ZHANGMINGMIAO/DIYSON-FOR-MDS/PCB/Snipaste_2023-03-19_16-48-15.png

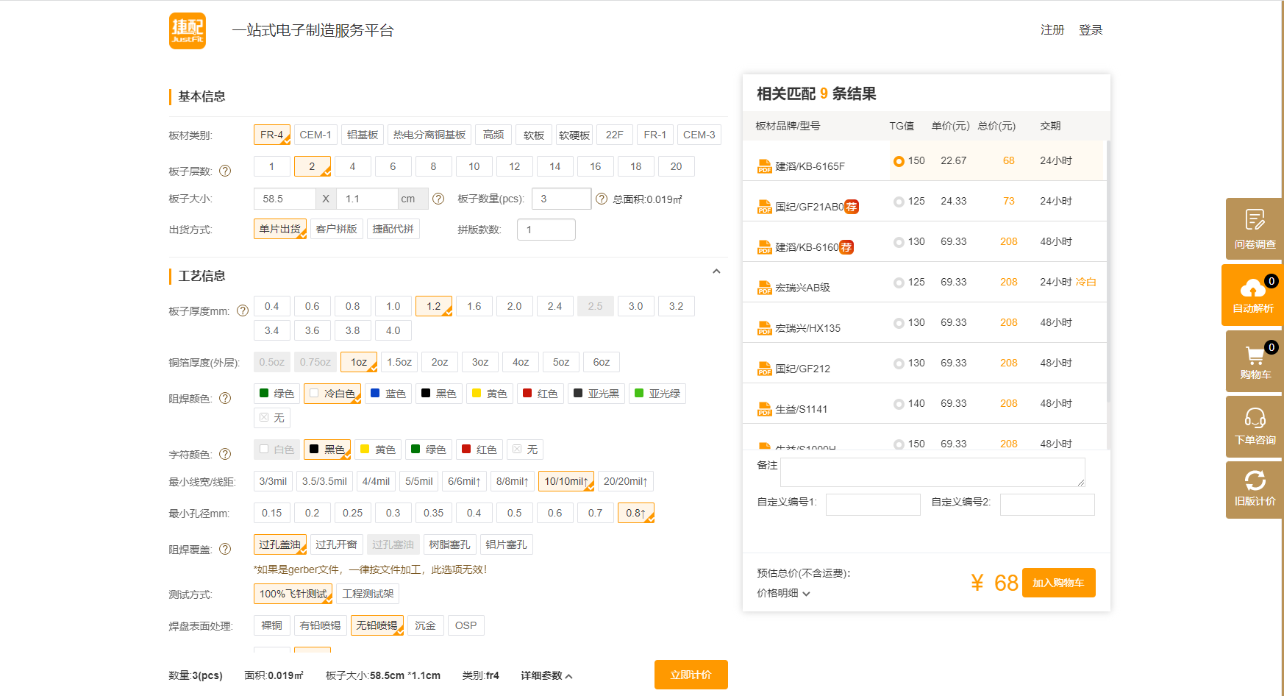
PCB/Snipaste_2023-03-19_16-48-15.png
