ZHANGMINGMIAO/DIYSON-FOR-MDS/PCB/Snipaste_2023-03-19_16-50-18.png

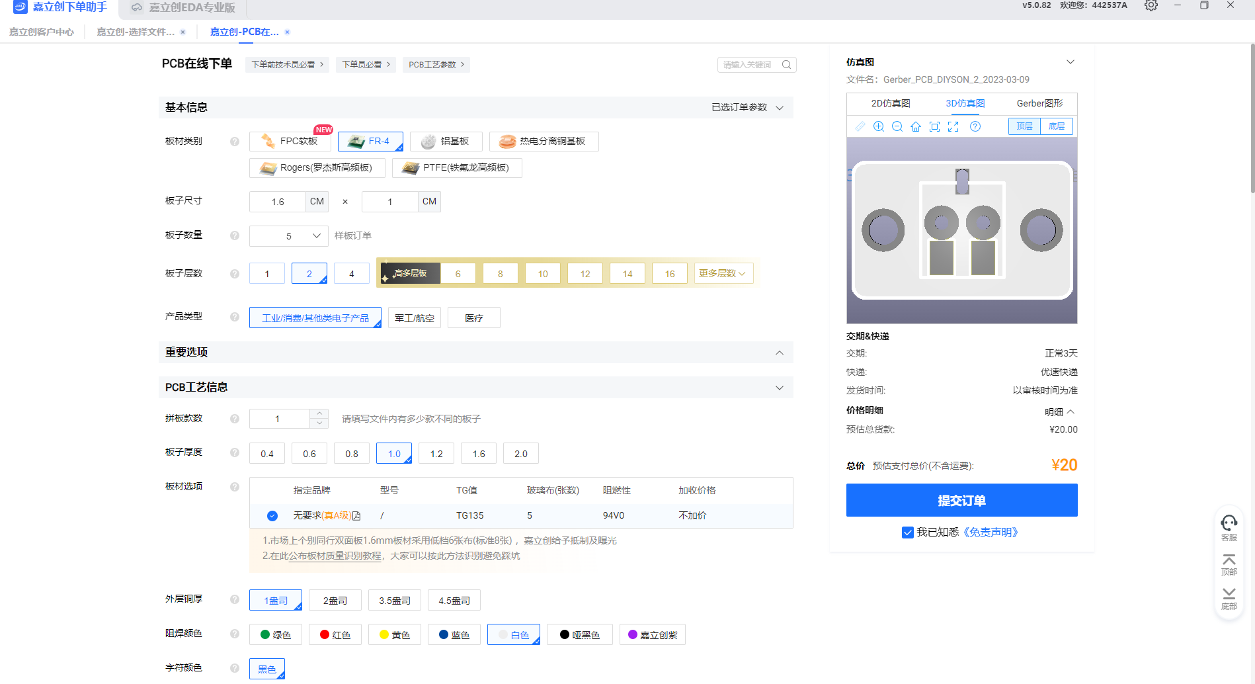
PCB/Snipaste_2023-03-19_16-50-18.png
