ZHANGMINGMIAO/DIYSON-FOR-MDS/Picture/DIYSON.10.png

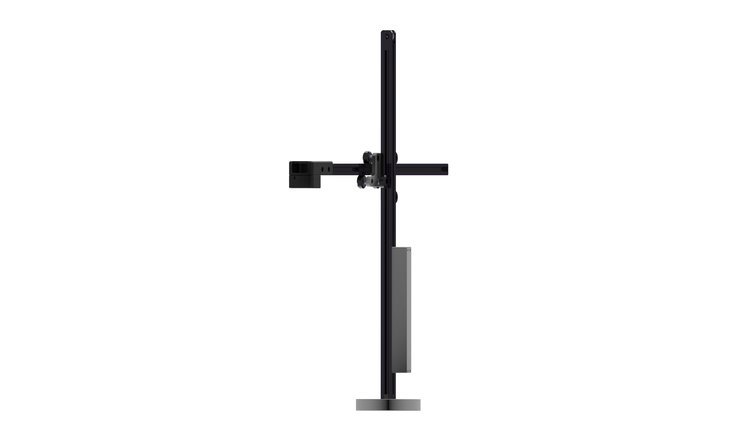
Picture/DIYSON.10.png
