ZHANGMINGMIAO/DIYSON-FOR-MDS/STL/Coutnterweight Enclosure.STL

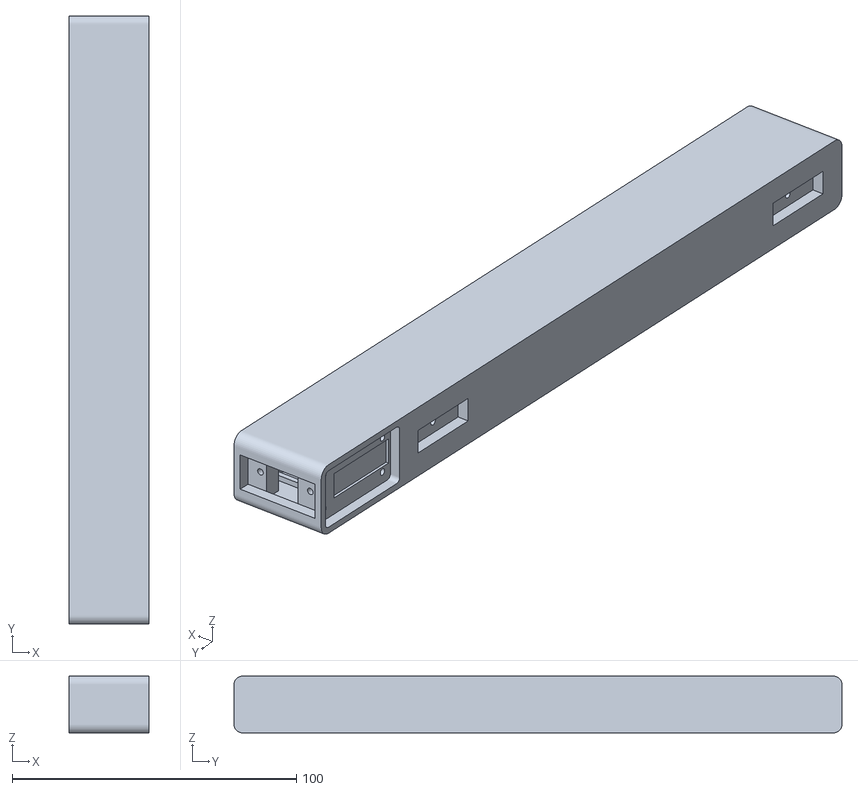
[picture p23: CAD file, 2023-05-03]
STL/Coutnterweight Enclosure.STL
28.0 x 214.0 x 20.0
