ZHANGMINGMIAO/DIYSON-FOR-MDS/STL/灯头底盖.STL

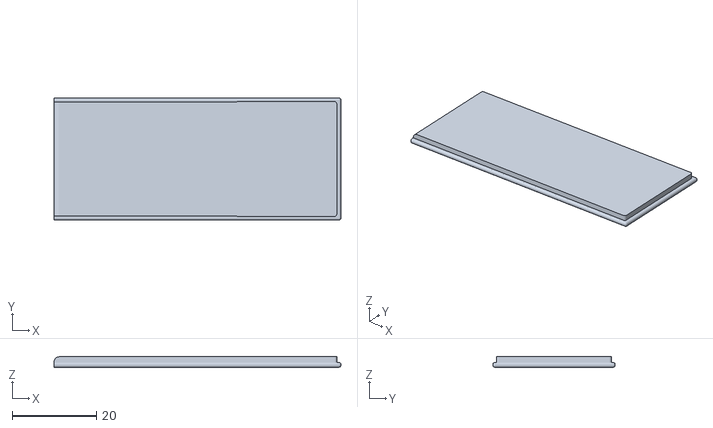
[picture p24: CAD file, 2023-05-03]
STL/灯头底盖.STL
68.0 x 29.0 x 2.50
