ZHANGMINGMIAO/DIYSON-FOR-MDS/slprt/Carriage2.SLDPRT

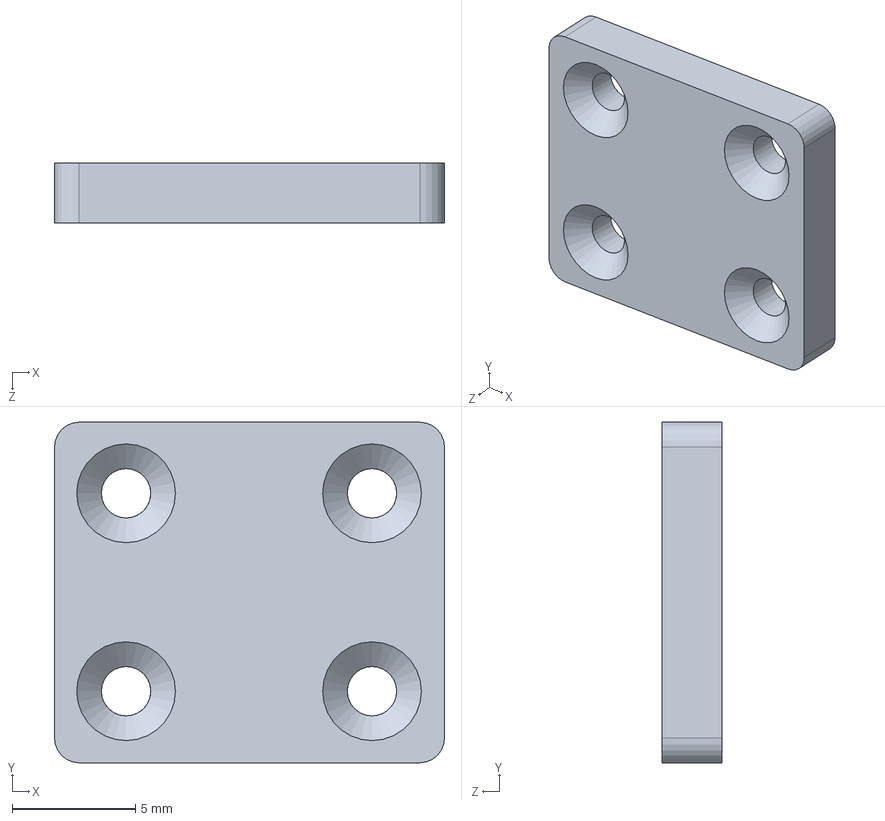
[picture p25: CAD file, 2023-05-03]
slprt/Carriage2.SLDPRT
15.8 x 13.8 x 2.45 mm
