ZHANGMINGMIAO/DIYSON-FOR-MDS/STL/灯头.STL

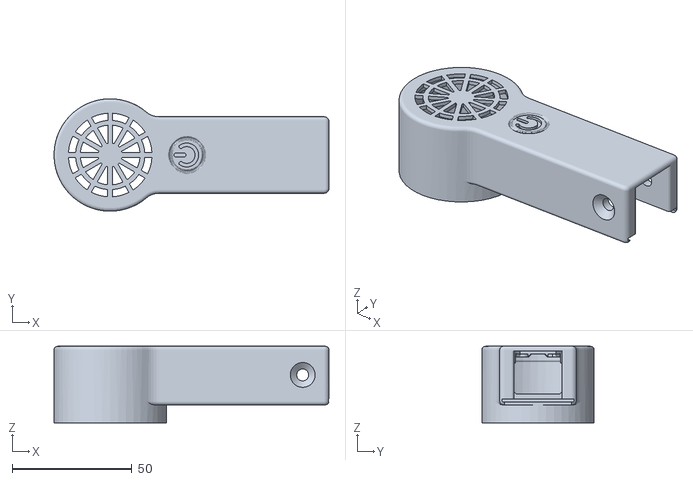
[picture p26: CAD file, 2023-05-03]
STL/灯头.STL
115.0 x 47.0 x 32.0
