ZHANGMINGMIAO/DIYSON-FOR-MDS/slprt/灯头底盖.sldprt

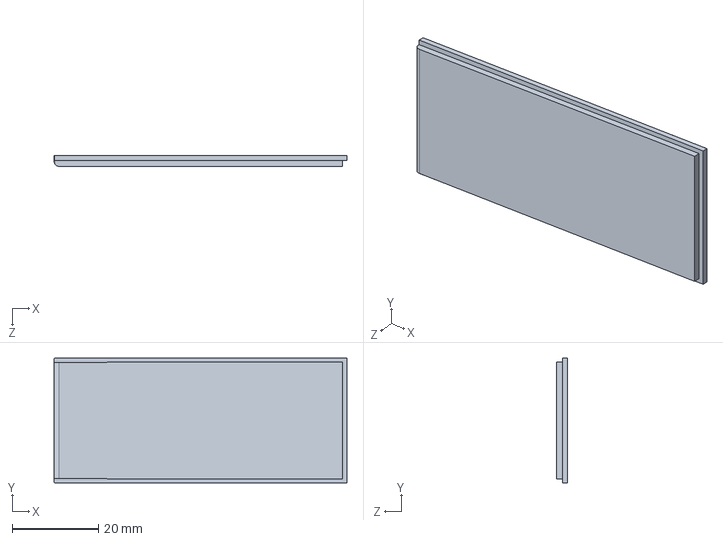
[picture p27: CAD file, 2023-05-03]
slprt/灯头底盖.sldprt
68.0 x 29.0 x 2.50 mm
