ZHANGMINGMIAO/DIYSON-FOR-MDS/slprt/Base2.sldprt

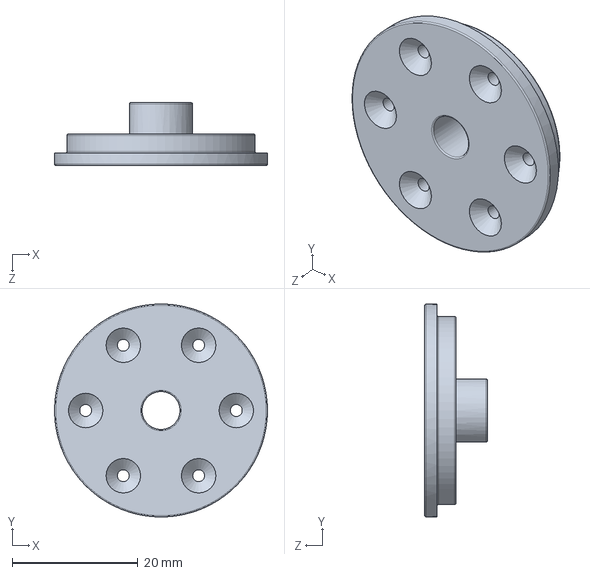
[picture p28: CAD file, 2023-05-03]
slprt/Base2.sldprt
33.9 x 33.9 x 10.0 mm
