ZHANGMINGMIAO/DIYSON-FOR-MDS/STL/Flex Tab.STL

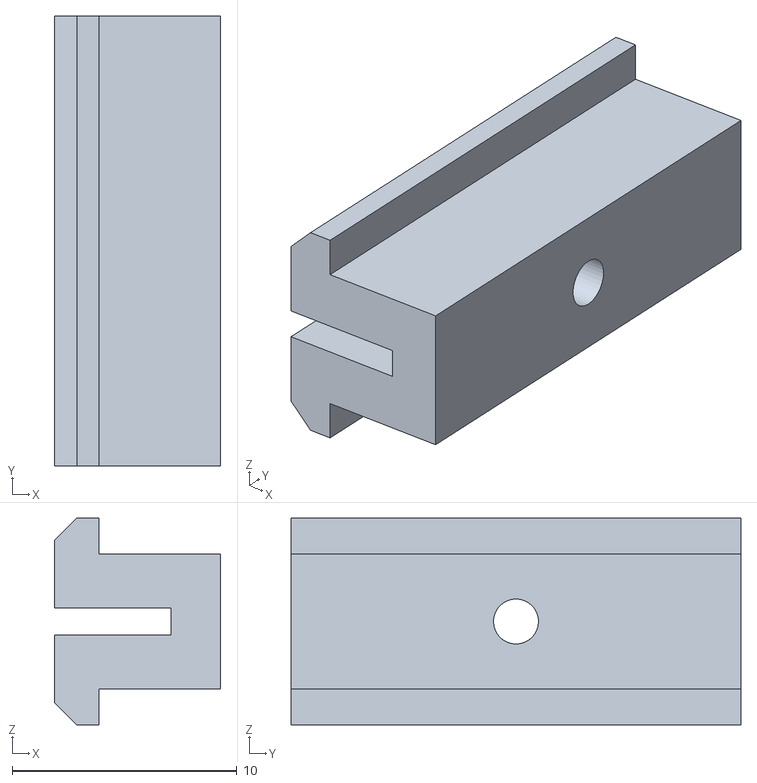
[picture p29: CAD file, 2023-03-19]
STL/Flex Tab.STL
7.40 x 20.0 x 9.20
