ZHANGMINGMIAO/DIYSON-FOR-MDS/STL/Pulley Mount.STL

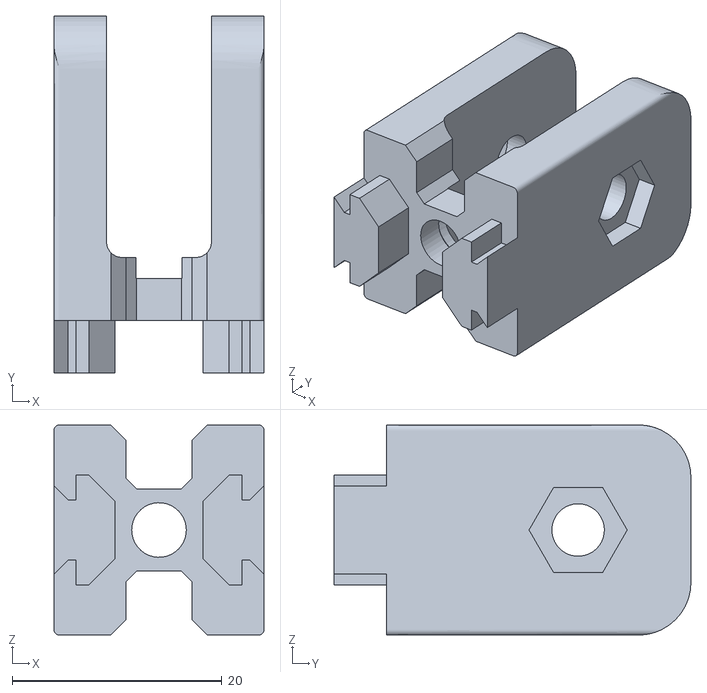
[picture p30: CAD file, 2023-03-16]
STL/Pulley Mount.STL
20.0 x 34.0 x 20.0
