ZHANGMINGMIAO/DIYSON-FOR-MDS/STL/End Cap.STL

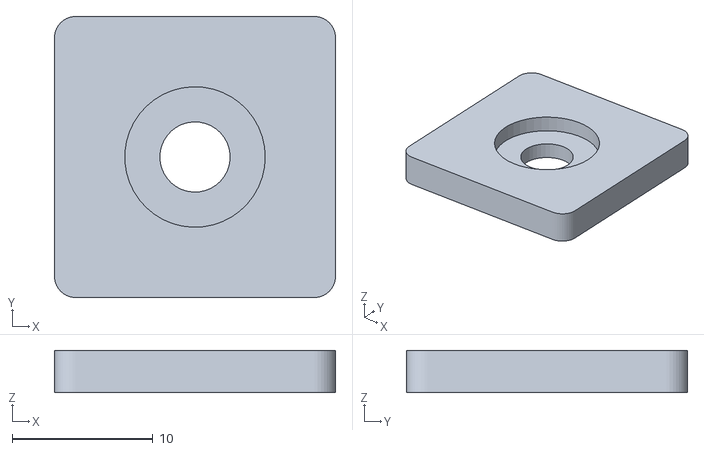
[picture p31: CAD file, 2023-03-16]
STL/End Cap.STL
20.0 x 20.0 x 3.00
