ZHANGMINGMIAO/DIYSON-FOR-MDS/STL/Counterweight Belt Clip.STL

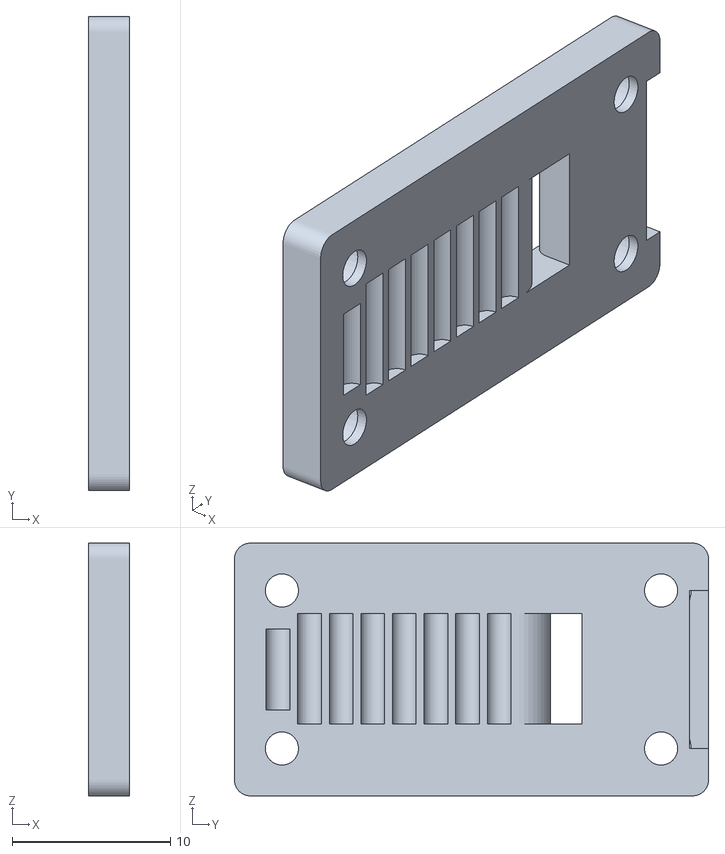
[picture p32: CAD file, 2023-03-16]
STL/Counterweight Belt Clip.STL
2.60 x 30.0 x 16.0
