ZHANGMINGMIAO/DIYSON-FOR-MDS/STL/Coutnterweight Lid.STL

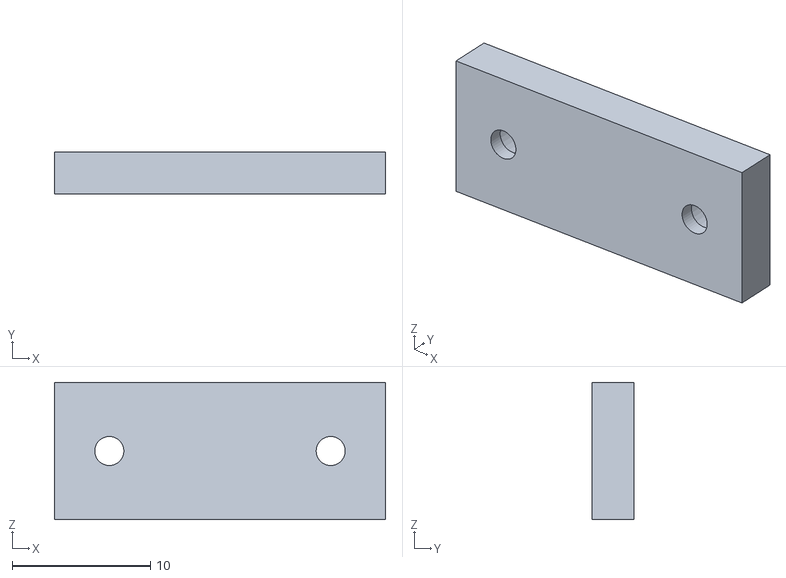
[picture p33: CAD file, 2023-03-16]
STL/Coutnterweight Lid.STL
23.9 x 3.00 x 9.92
