ZHANGMINGMIAO/DIYSON-FOR-MDS/slprt/2020V 铝型材.sldprt

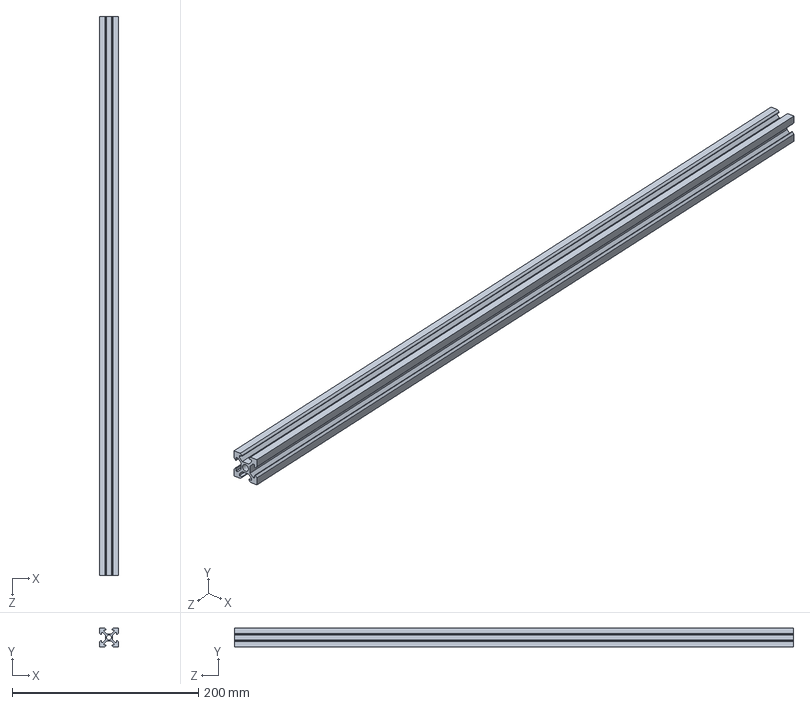
[picture p34: CAD file, 2023-03-16]
slprt/2020V 铝型材.sldprt
20.0 x 20.0 x 600.0 mm
