ZHANGMINGMIAO/DIYSON-FOR-MDS/slprt/6206ZZ轴承.SLDPRT

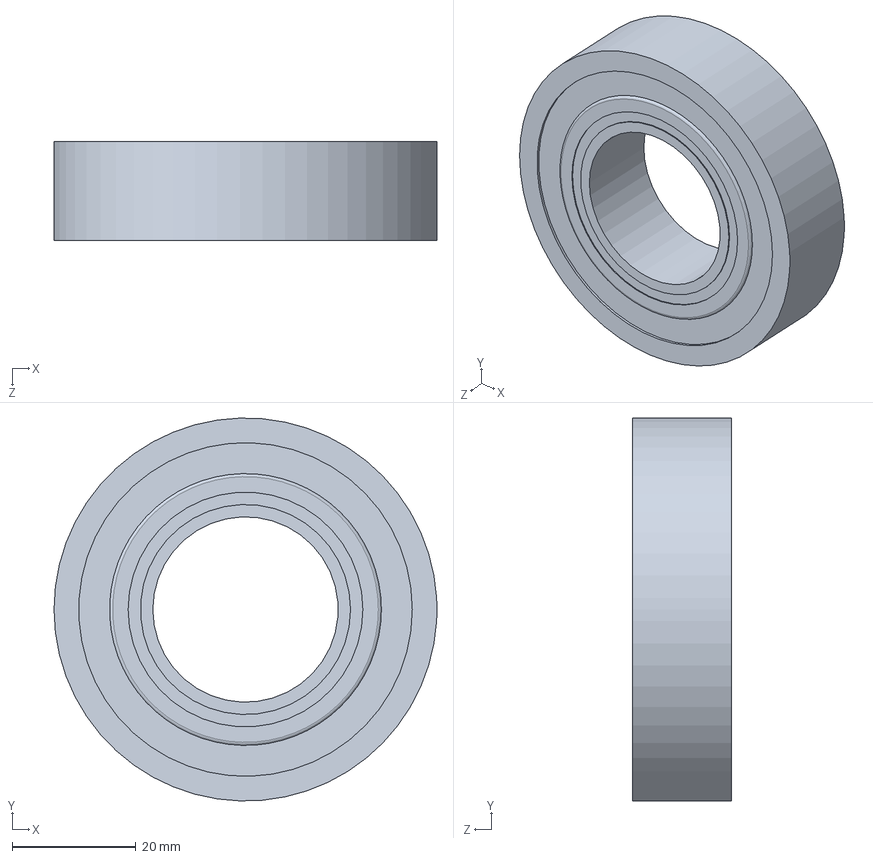
[picture p35: CAD file, 2023-03-16]
slprt/6206ZZ轴承.SLDPRT
62.0 x 62.0 x 16.0 mm
