ZHANGMINGMIAO/DIYSON-FOR-MDS/slprt/按键盖板.sldprt

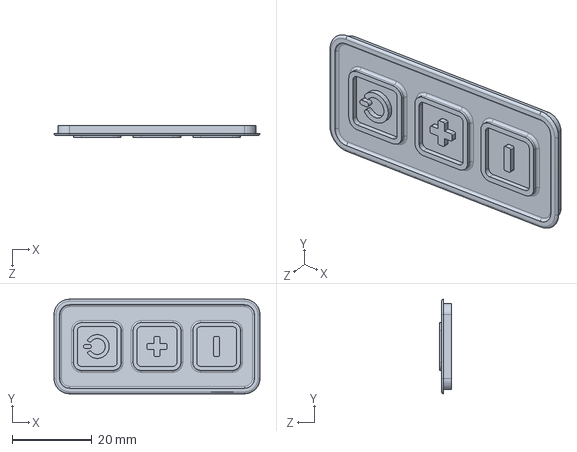
[picture p36: CAD file, 2023-03-16]
slprt/按键盖板.sldprt
51.8 x 23.8 x 3.00 mm
