ZHANGMINGMIAO/DIYSON-FOR-MDS/slprt/散热器3820.SLDPRT

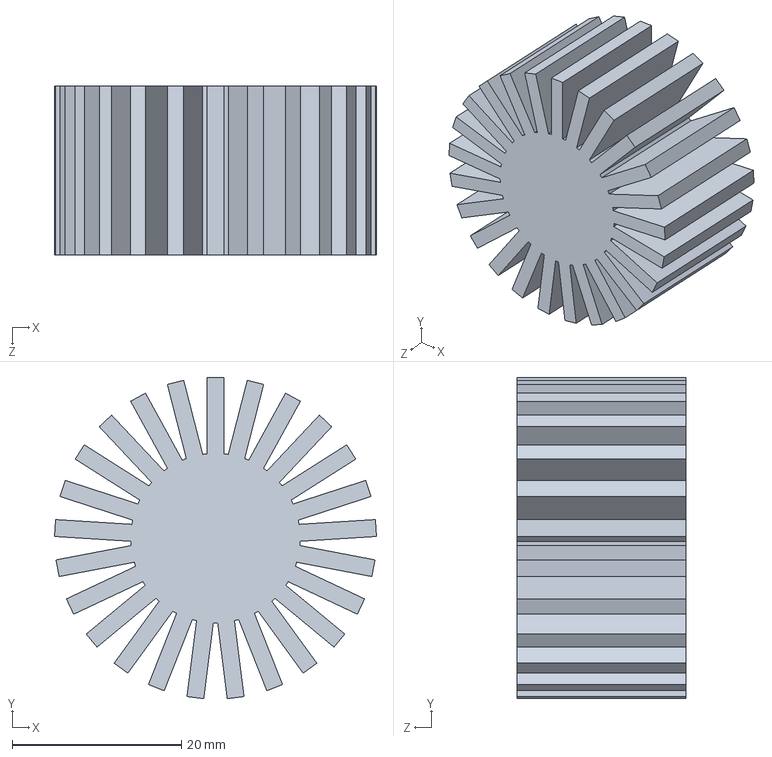
[picture p37: CAD file, 2023-03-16]
slprt/散热器3820.SLDPRT
38.0 x 37.9 x 20.0 mm
