ZHANGMINGMIAO/DIYSON-FOR-MDS/slprt/风扇3010.SLDPRT

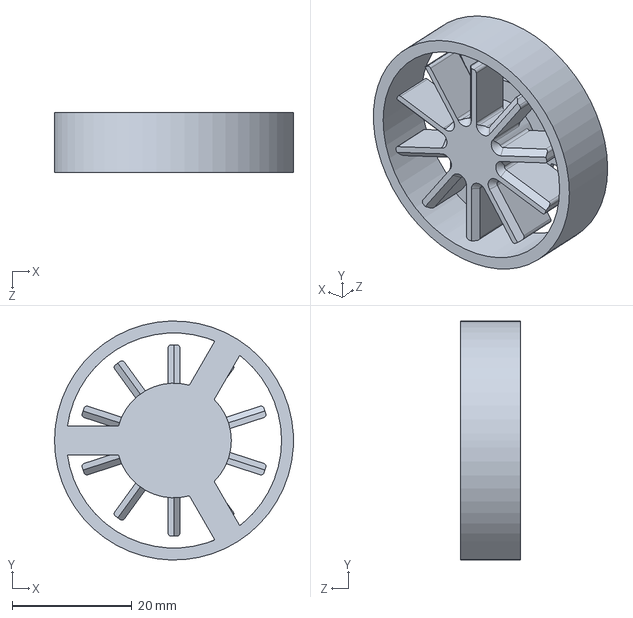
[picture p38: CAD file, 2023-03-16]
slprt/风扇3010.SLDPRT
40.0 x 40.0 x 10.0 mm
