ZHANGMINGMIAO/DIYSON-FOR-MDS/slprt/DC.SLDPRT

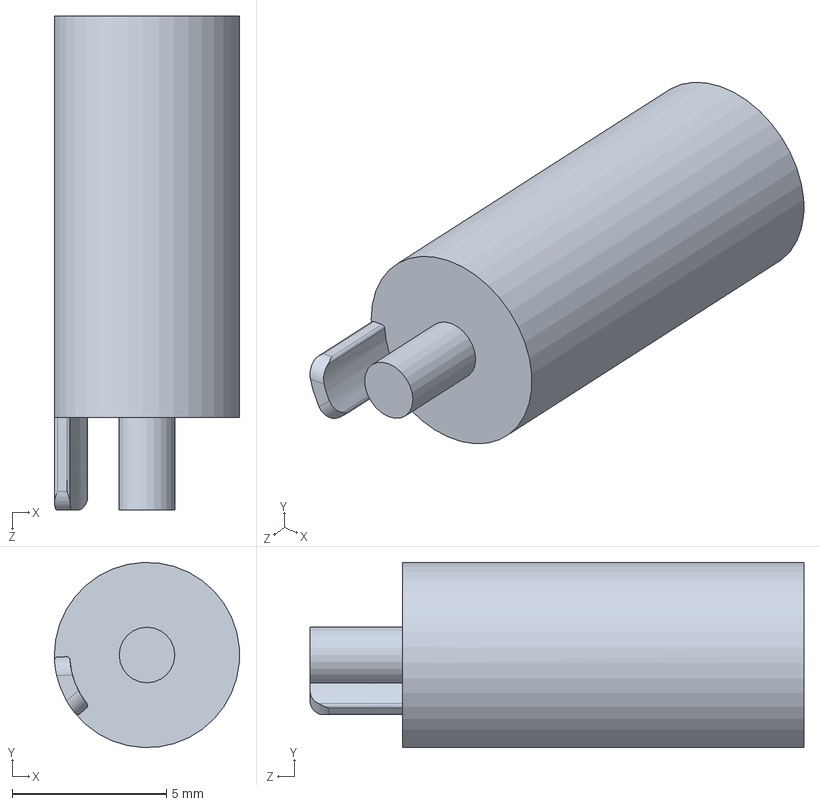
[picture p39: CAD file, 2023-03-16]
slprt/DC.SLDPRT
6.00 x 5.99 x 16.0 mm
